BigCorvus/SMA-Q2_replacement_board/20191017_104635.jpg

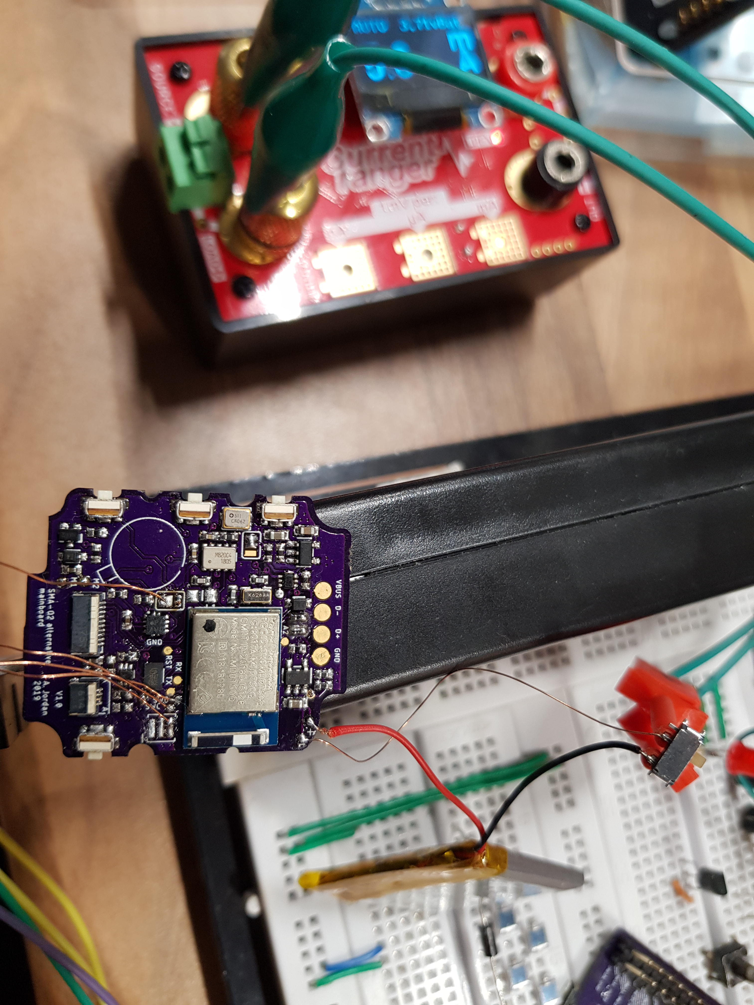
20191017_104635.jpg
